Caraffa-git/SD-Interrupter/images/img1.jpg

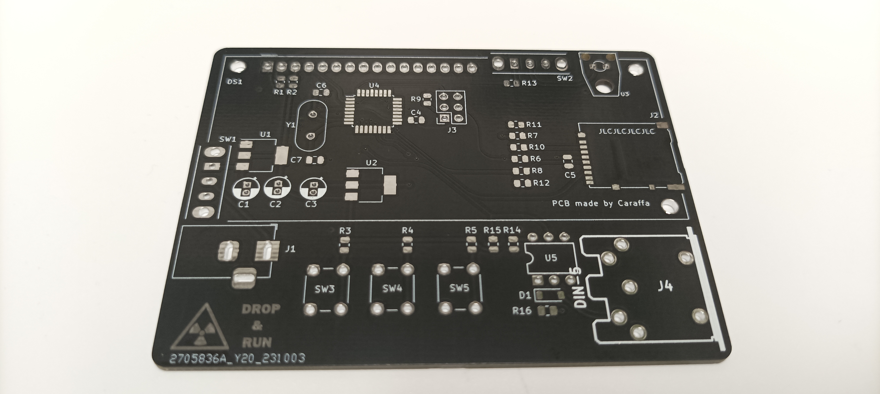
images/img1.jpg
