Caraffa-git/SD-Interrupter/images/img2.jpg

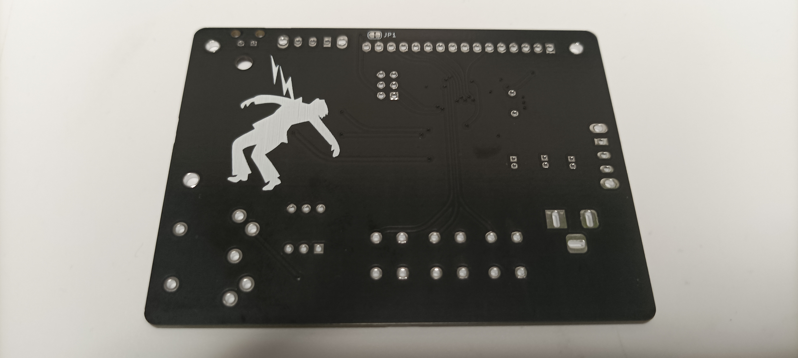
images/img2.jpg
