Caraffa-git/SD-Interrupter/images/img3.jpg

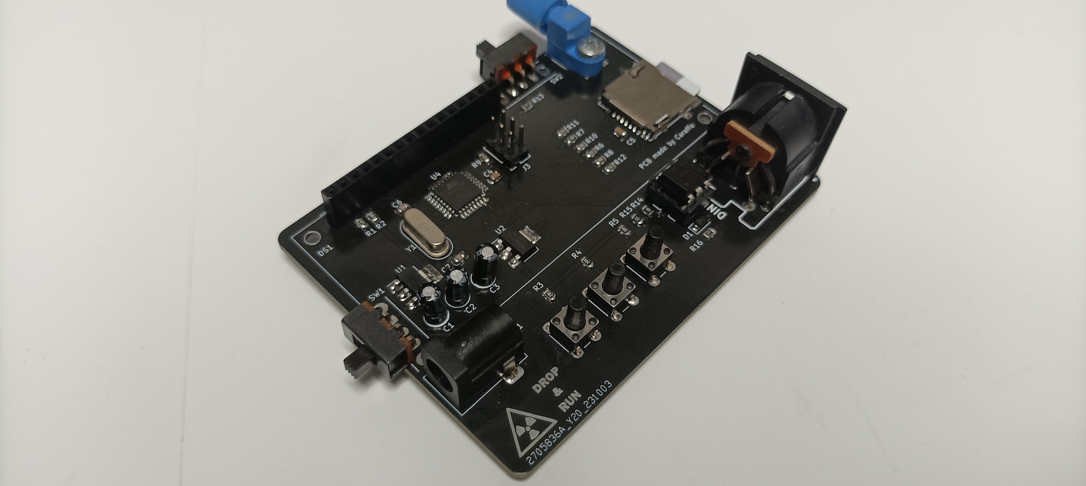
images/img3.jpg
