Caraffa-git/SD-Interrupter/images/img4.jpg

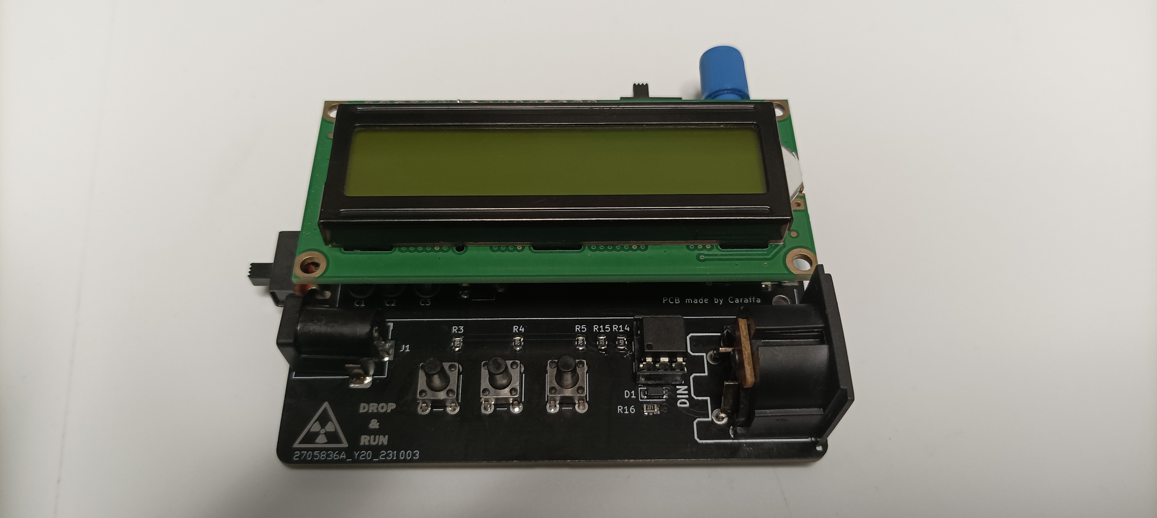
images/img4.jpg
