Caraffa-git/SD-Interrupter/software/Software (2017)/src/main/constants.h

/*
 * constants.h
 * Contains defined constants, user-modifiable macros, and structures
 * Read the manual to see what to modify
 */
 
#ifndef __CONSTANTS_H

#include "system.h"

//#define DEBUG

/****Coil-dependent configuration variables: change these to match your coil****/

//multiply the pulsewidths by this constant, good for quick 'n dirty scaling
#define LOOKUP_TABLE_SCALE 3

//minimum on-time, in microseconds
#define MIN_ON_TIME 10

//on-times in microseconds, don't forget to multiply by LOOKUP_TABLE_SCALE!
#define ON_TIME_ARRAY_LENGTH 26
static byte on_times[] = 
{33, 33, 33, 33, 27, 23, 20, 20, 18, 17, 16, 15, 14, 13, 12, 11, 10, 9, 8, 8, 8, 8, 8, 8, 8, 8};

/****End coil config variables****/

/****Instrument-dependent configuration variables: change to match your MIDI device****/

//sustain time, in microseconds
#define SUSTAIN_TIME 750000
#define SUSTAIN_TIME_OVER_256 2930

//lets us change the way velocity mapping works (linear, LUT, something else...)
#define map_velocity(v) (127 + v / 2)

//map the sustain time as well
#define map_sustain(t) ((long) (t) / SUSTAIN_TIME_OVER_256)
/****End instrument config variables****/

/****System stuff****/
#define FILE_BUFFER_SIZE 256

#define MMC_CS 10

#ifdef DEBUG
  #define RS 8
  #define EN 9
  #define D4 4
  #define D5 5
  #define D6 6
  #define D7 7
#else
  #define BTN_UP A0
  #define BTN_OK A2
  #define BTN_DN A3
  #define RS 4
  #define EN 5
  #define D4 6
  #define D5 7
  #define D6 8
  #define D7 9
#endif

//don't mess with these!
#define BITS_8 256
#define BITS_16 65536
#define TIMER_2_PERIOD_MAX 16000

static unsigned int base[] = {220, 233, 247, 262, 277, 294, 311, 330, 349, 370, 392, 415};
static unsigned char pow2[] = {1, 2, 4, 8, 16, 32};
static char chex[] = {'0', '1', '2', '3', '4', '5', '6', '7', '8', '9', 'a', 'b', 'c', 'd', 'e', 'f'};
static unsigned char block[8] = {0xff, 0xff, 0xff, 0xff, 0xff, 0xff, 0xff, 0xff};
static unsigned char arrow[8] = {~0x0f, ~0x07, ~0x03, ~0x01, ~0x03, ~0x07, ~0x0f, 0x00};

#define btnRIGHT  0
#define btnUP     1
#define btnDOWN   2
#define btnLEFT   3
#define btnSELECT 4
#define btnNONE   5

#define MENU_SDCARD 0
#define MENU_FIXED  2
#define MENU_LIVE   1
#define MENU_BURST 3

#define __CONSTANTS_H
#endif
